olegamobile/sheriff3d/chez_downloads/calife_article_coinb.GIF

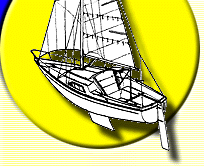
chez_downloads/calife_article_coinb.GIF
