olegamobile/sheriff3d/downloaded_assets/assets/photos/axesafran.jpg

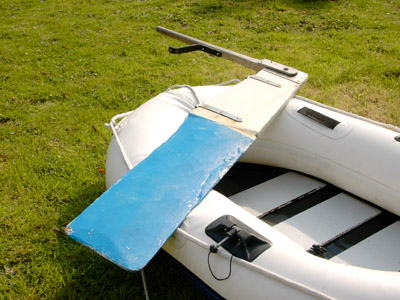
downloaded_assets/assets/photos/axesafran.jpg
