olegamobile/sheriff3d/downloaded_assets/assets/photos/Constance_I.jpg

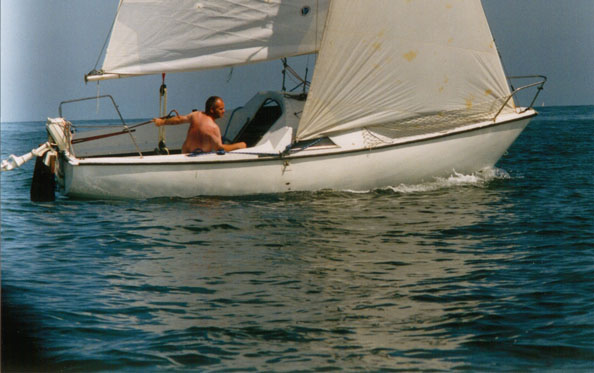
downloaded_assets/assets/photos/Constance_I.jpg
