olegamobile/sheriff3d/downloaded_assets/assets/photos/farfelu.jpg

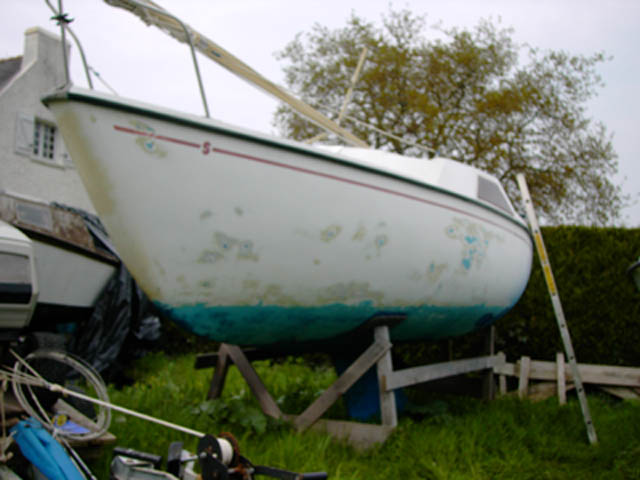
downloaded_assets/assets/photos/farfelu.jpg
