olegamobile/sheriff3d/downloaded_assets/assets/photos/ladesirade.jpg

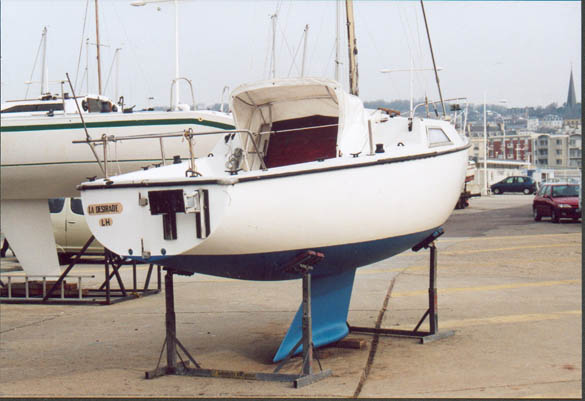
downloaded_assets/assets/photos/ladesirade.jpg
