olegamobile/sheriff3d/downloaded_assets/assets/photos/mouillage_Aix.jpg

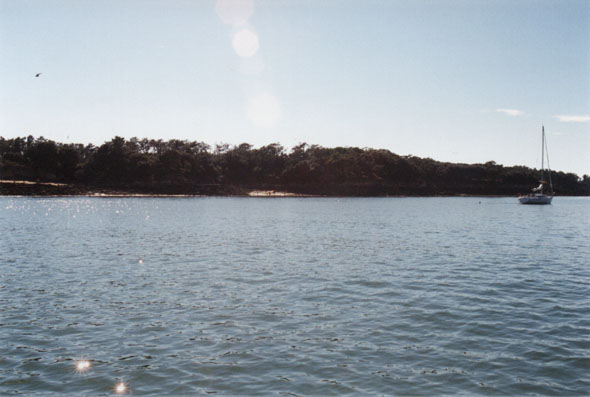
downloaded_assets/assets/photos/mouillage_Aix.jpg
