olegamobile/sheriff3d/downloaded_assets/assets/photos/mouro1.jpg

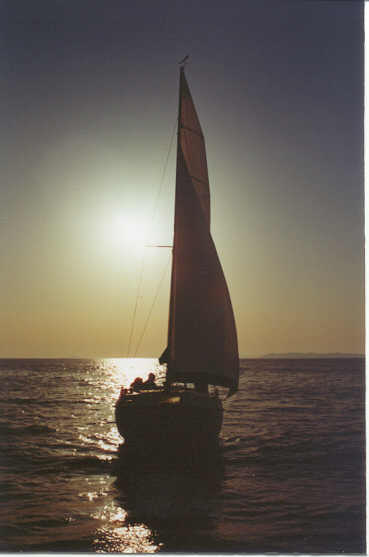
downloaded_assets/assets/photos/mouro1.jpg
