olegamobile/sheriff3d/downloaded_assets/assets/photos/mouro2.jpg

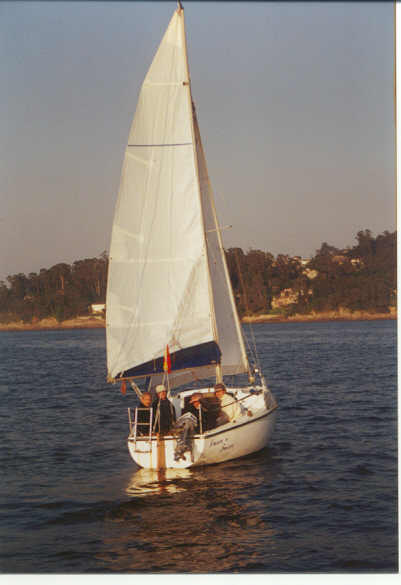
downloaded_assets/assets/photos/mouro2.jpg
