olegamobile/sheriff3d/downloaded_assets/assets/photos/noddi1.jpg

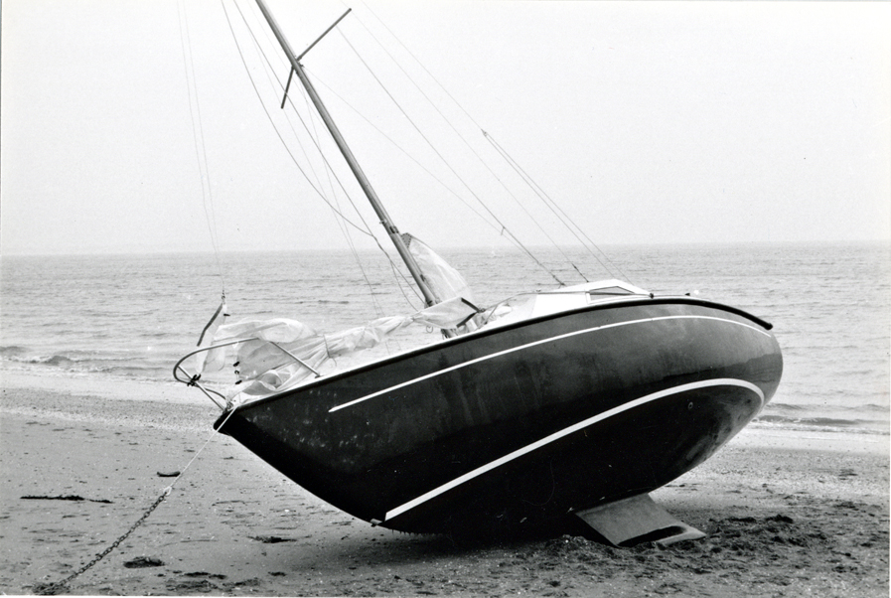
downloaded_assets/assets/photos/noddi1.jpg
