olegamobile/sheriff3d/downloaded_assets/assets/photos/noddi2.jpg

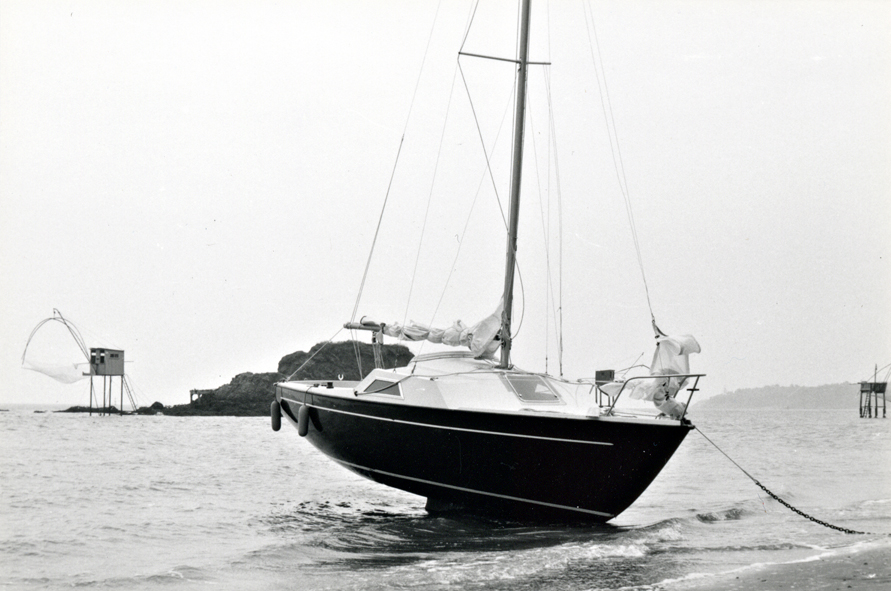
downloaded_assets/assets/photos/noddi2.jpg
