olegamobile/sheriff3d/downloaded_assets/assets/photos/port_RT_Arriere.jpg

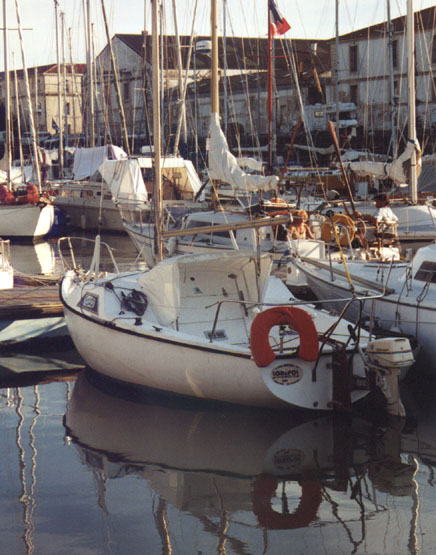
downloaded_assets/assets/photos/port_RT_Arriere.jpg
