olegamobile/sheriff3d/downloaded_assets/assets/photos/port_RT_pont.jpg

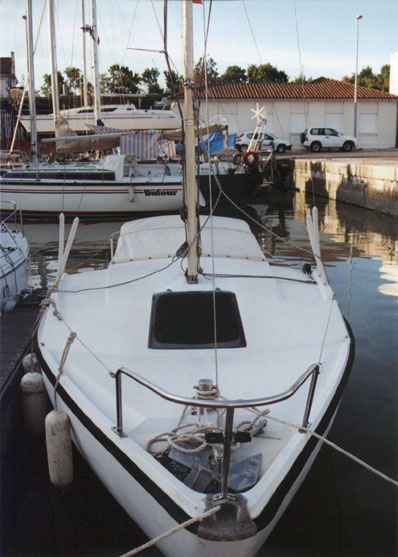
downloaded_assets/assets/photos/port_RT_pont.jpg
