olegamobile/sheriff3d/downloaded_assets/assets/photos/samoa_ii.jpg

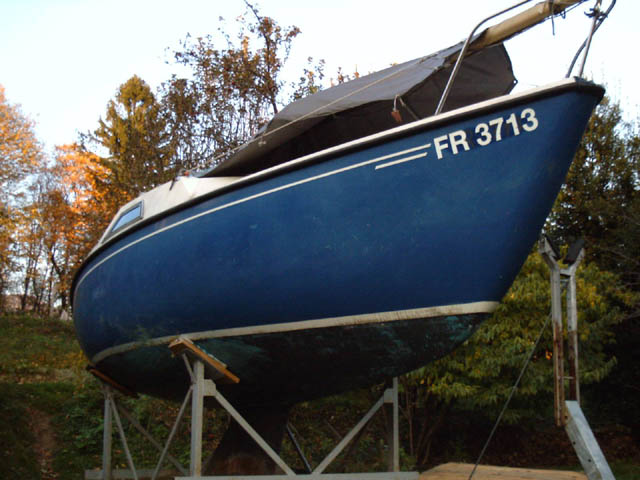
downloaded_assets/assets/photos/samoa_ii.jpg
