olegamobile/sheriff3d/extracted_pdf_assets/Bateaux_jui73/p1_1__im1.png

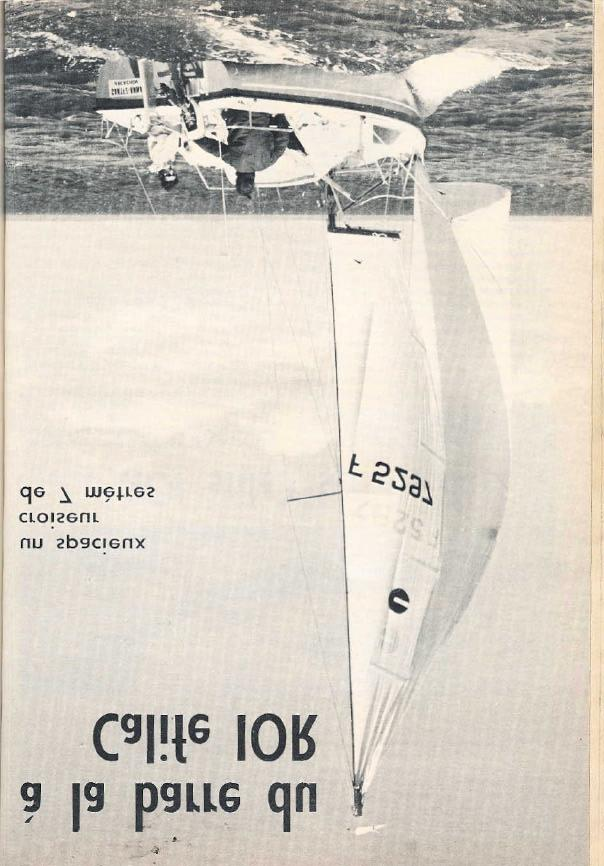
extracted_pdf_assets/Bateaux_jui73/p1_1__im1.png
