olegamobile/sheriff3d/extracted_pdf_assets/Bateaux_jui73/p1_corrected.png

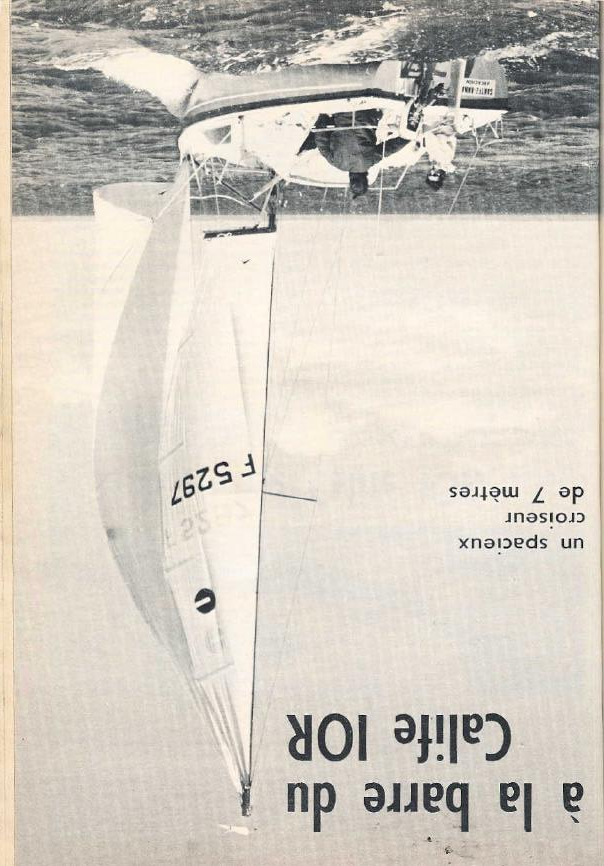
extracted_pdf_assets/Bateaux_jui73/p1_corrected.png
