olegamobile/sheriff3d/extracted_pdf_assets/Bateaux_jui73/p2_1__im2.png

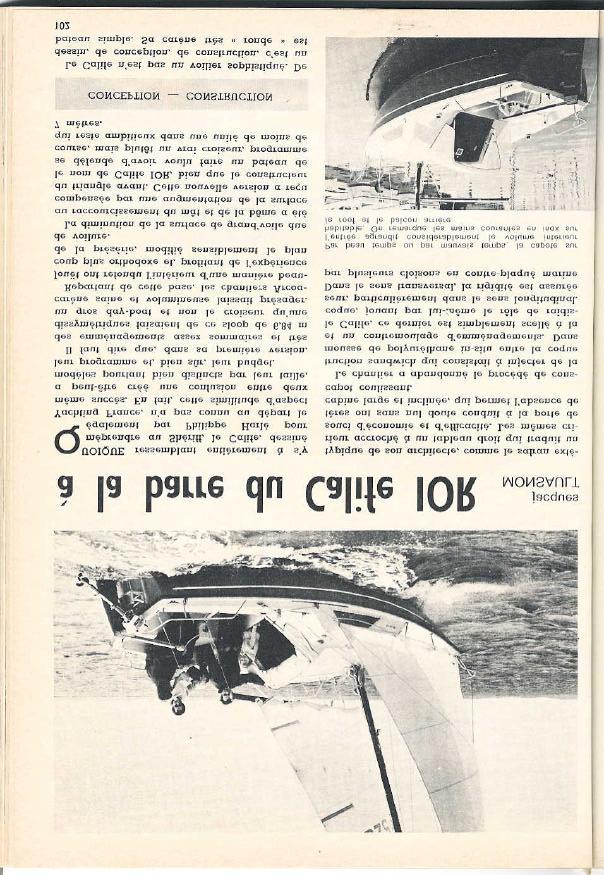
extracted_pdf_assets/Bateaux_jui73/p2_1__im2.png
