olegamobile/sheriff3d/extracted_pdf_assets/Bateaux_jui73/p3_1__im3.png

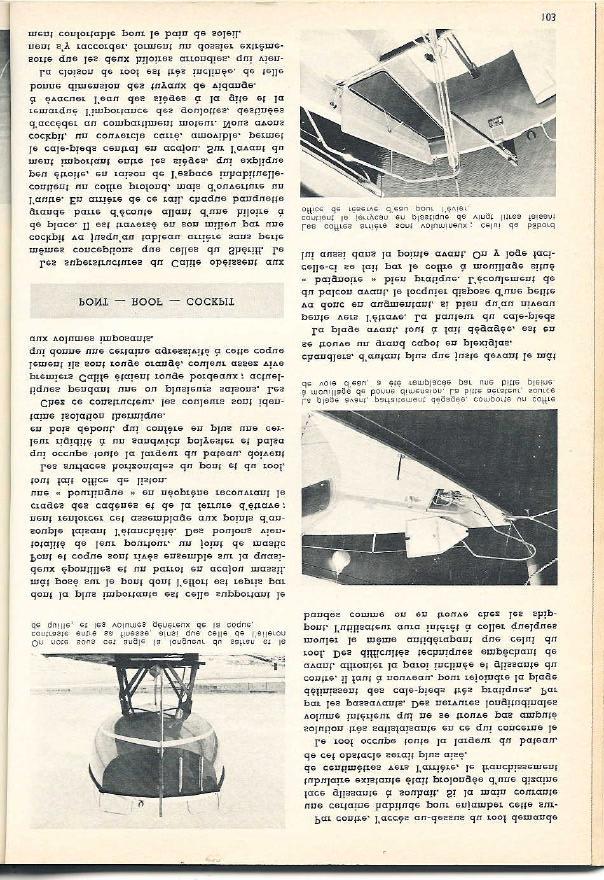
extracted_pdf_assets/Bateaux_jui73/p3_1__im3.png
