olegamobile/sheriff3d/extracted_pdf_assets/Bateaux_jui73/p7_1__im7.png

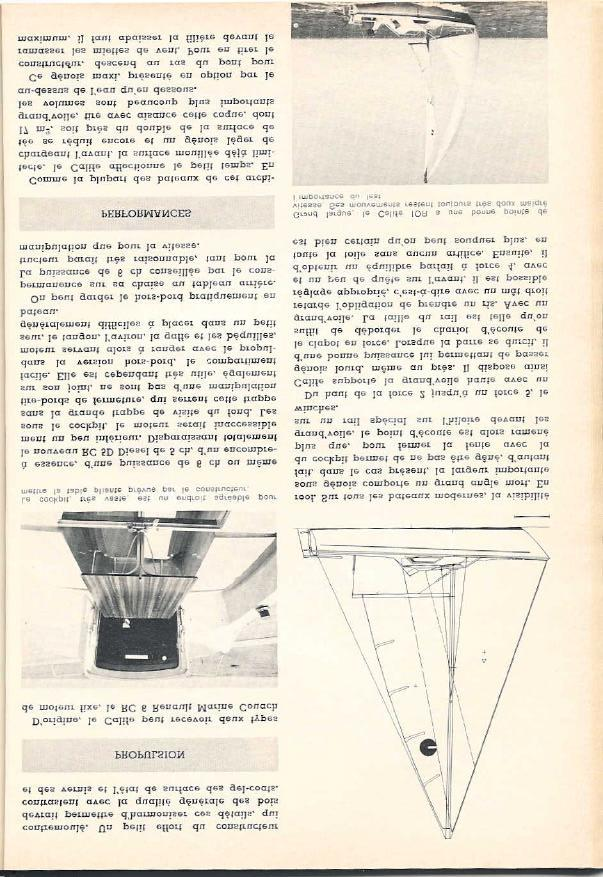
extracted_pdf_assets/Bateaux_jui73/p7_1__im7.png
