olegamobile/sheriff3d/extracted_pdf_assets/Bateaux_jui73/p8_1__im8.png

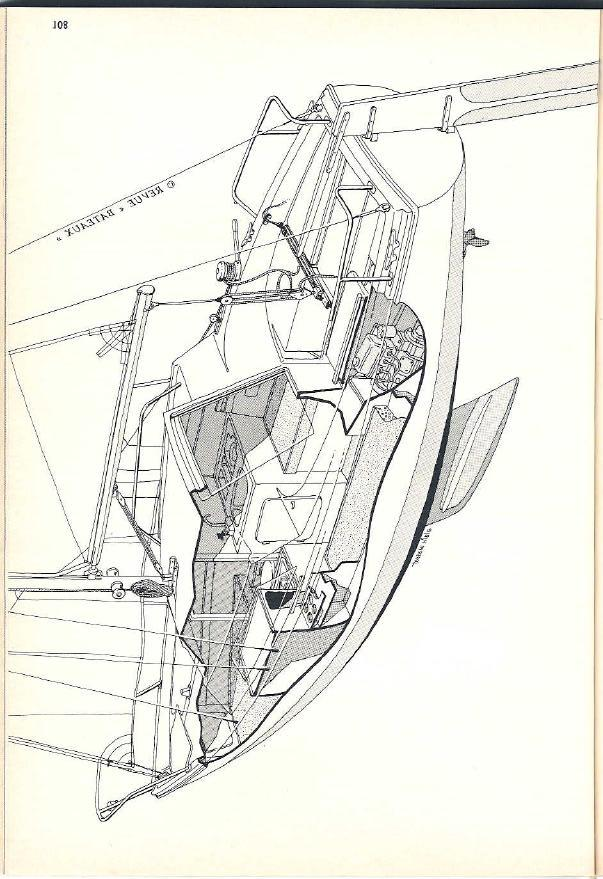
extracted_pdf_assets/Bateaux_jui73/p8_1__im8.png
