olegamobile/sheriff3d/extracted_pdf_assets/Bateaux_jui73/p10_1__im10.png

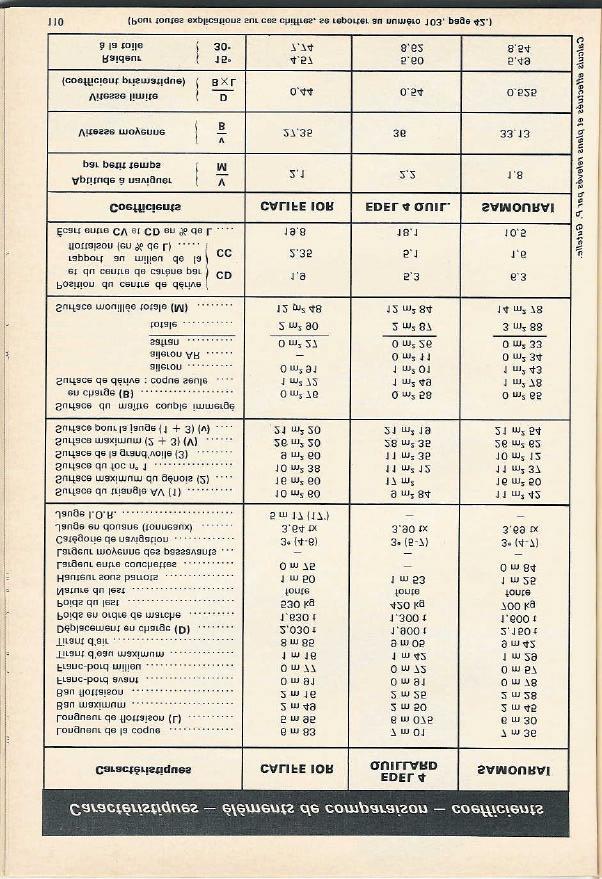
extracted_pdf_assets/Bateaux_jui73/p10_1__im10.png
