olegamobile/sheriff3d/extracted_pdf_assets/Bateaux_oct69/annotated_body_plan.png

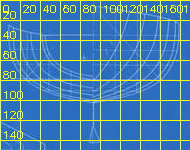
extracted_pdf_assets/Bateaux_oct69/annotated_body_plan.png
