olegamobile/sheriff3d/extracted_pdf_assets/Bateaux_oct69/annotated_half_breadth.png

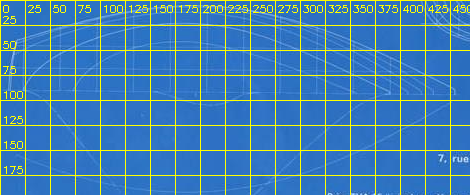
extracted_pdf_assets/Bateaux_oct69/annotated_half_breadth.png
