olegamobile/sheriff3d/extracted_pdf_assets/Bateaux_oct69/annotated_profile.png

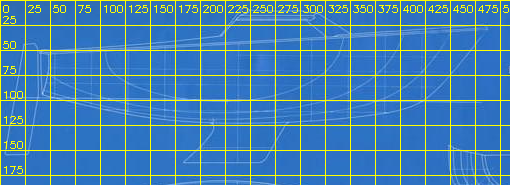
extracted_pdf_assets/Bateaux_oct69/annotated_profile.png
