olegamobile/sheriff3d/extracted_pdf_assets/Bateaux_oct69/crop_half_breadth.png

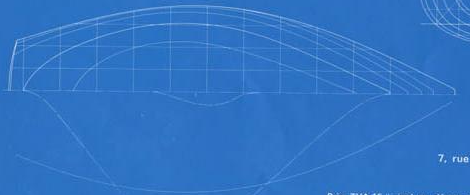
extracted_pdf_assets/Bateaux_oct69/crop_half_breadth.png
