olegamobile/sheriff3d/extracted_pdf_assets/Bateaux_oct69/crop_profile.png

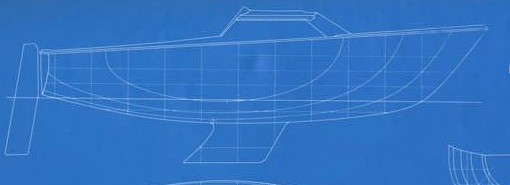
extracted_pdf_assets/Bateaux_oct69/crop_profile.png
