olegamobile/sheriff3d/extracted_pdf_assets/Bateaux_oct69/lines_plan_oriented.png

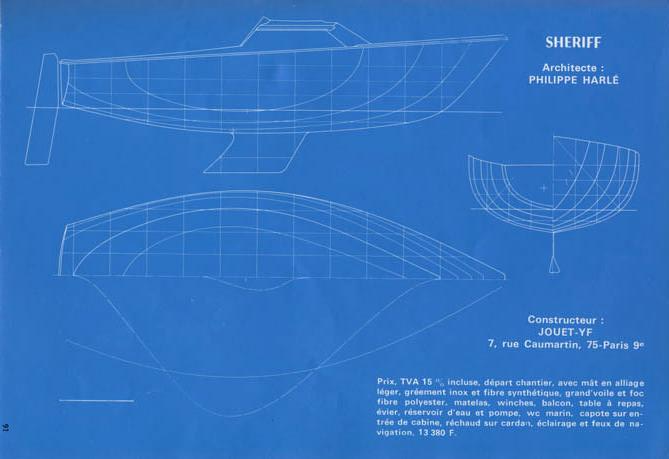
extracted_pdf_assets/Bateaux_oct69/lines_plan_oriented.png
