olegamobile/sheriff3d/extracted_pdf_assets/Bateaux_oct69/p1_1__im1.png

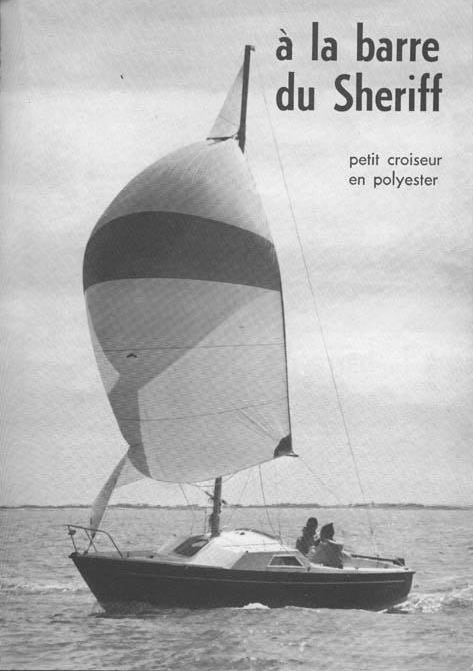
extracted_pdf_assets/Bateaux_oct69/p1_1__im1.png
