olegamobile/sheriff3d/extracted_pdf_assets/Bateaux_oct69/p4_1__im4.png

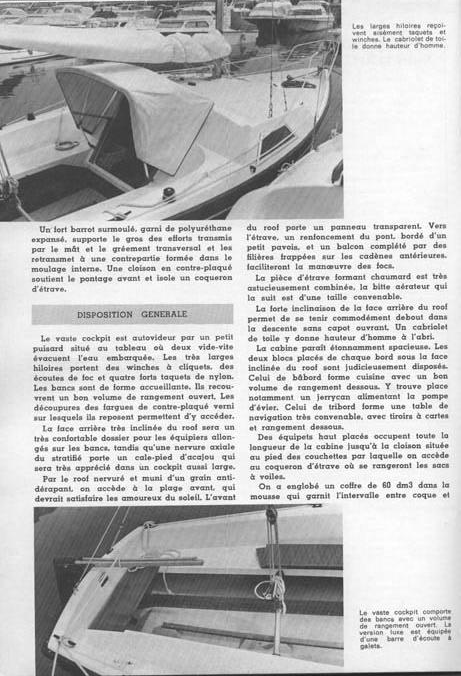
extracted_pdf_assets/Bateaux_oct69/p4_1__im4.png
