olegamobile/sheriff3d/extracted_pdf_assets/Bateaux_oct69/p5_1__im5.png

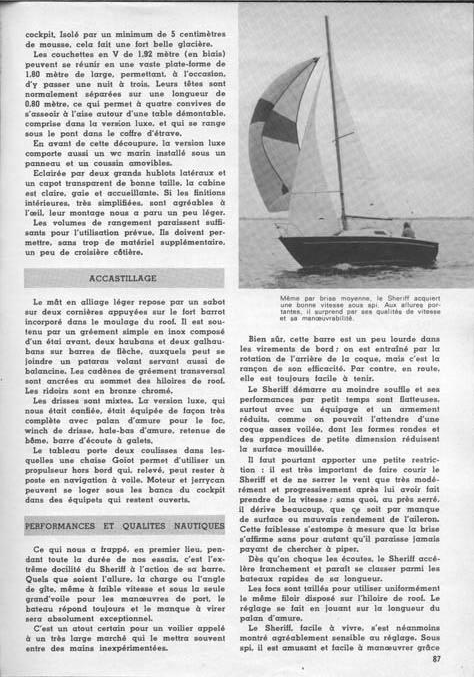
extracted_pdf_assets/Bateaux_oct69/p5_1__im5.png
