olegamobile/sheriff3d/extracted_pdf_assets/Bateaux_oct69/p6_1__im6.png

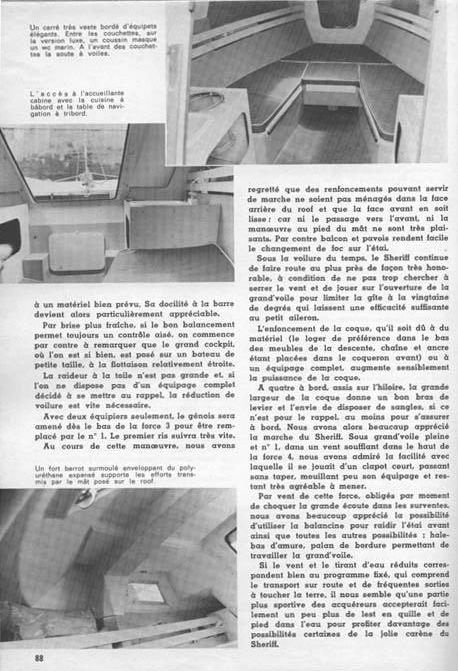
extracted_pdf_assets/Bateaux_oct69/p6_1__im6.png
