olegamobile/sheriff3d/extracted_pdf_assets/Bateaux_oct69/p9_1__im9.png

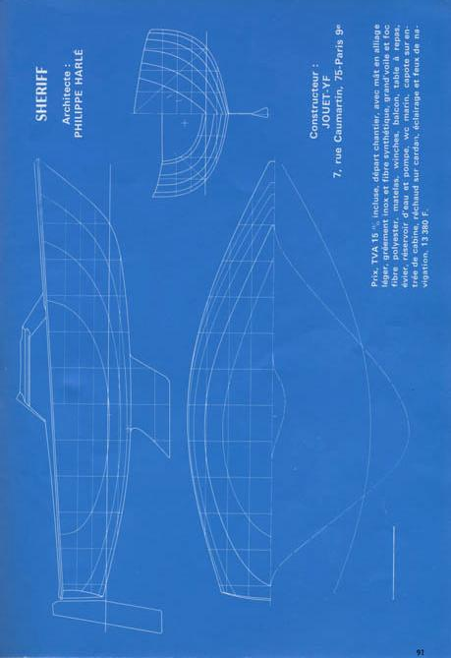
extracted_pdf_assets/Bateaux_oct69/p9_1__im9.png
