olegamobile/sheriff3d/extracted_pdf_assets/Bateaux_oct69/p11_1__im11.png

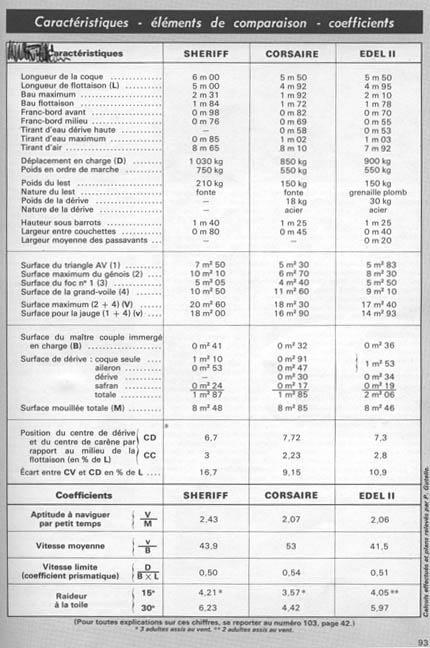
extracted_pdf_assets/Bateaux_oct69/p11_1__im11.png
