olegamobile/sheriff3d/extracted_pdf_assets/Bateaux_oct69/white_lines.png

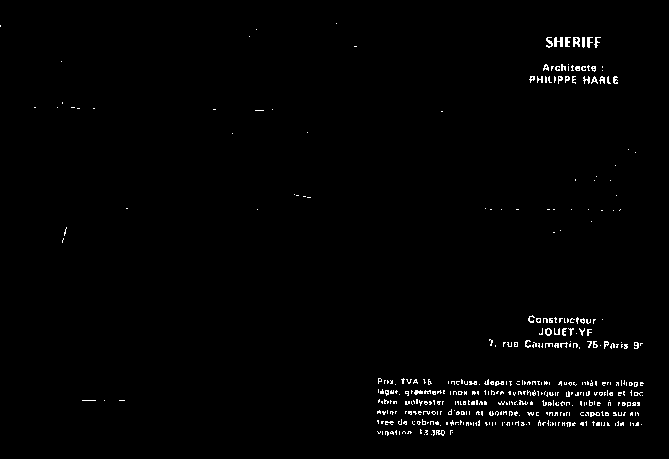
extracted_pdf_assets/Bateaux_oct69/white_lines.png
