olegamobile/sheriff3d/extracted_pdf_assets/manuel/p2_1__im1.png

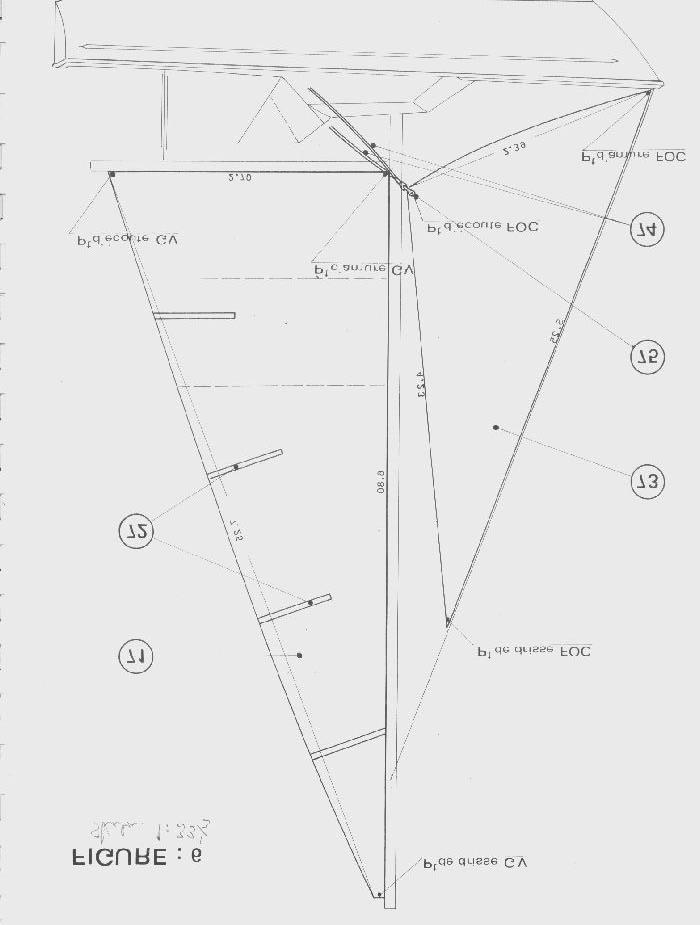
extracted_pdf_assets/manuel/p2_1__im1.png
