olegamobile/sheriff3d/extracted_pdf_assets/manuel/p3_1__im2.png

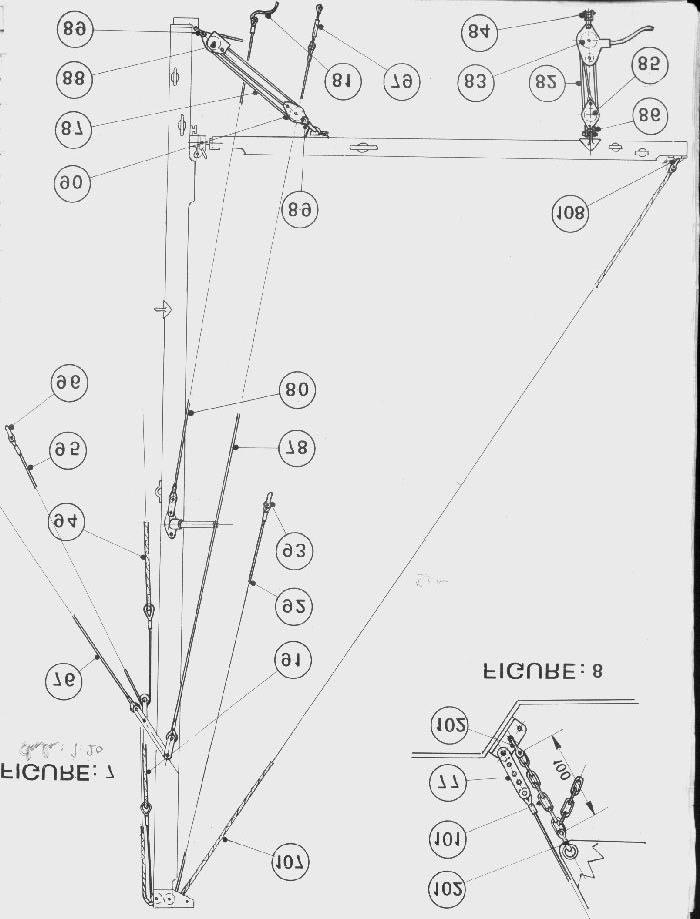
extracted_pdf_assets/manuel/p3_1__im2.png
