olegamobile/sheriff3d/extracted_pdf_assets/manuel/p4_1__im3.png

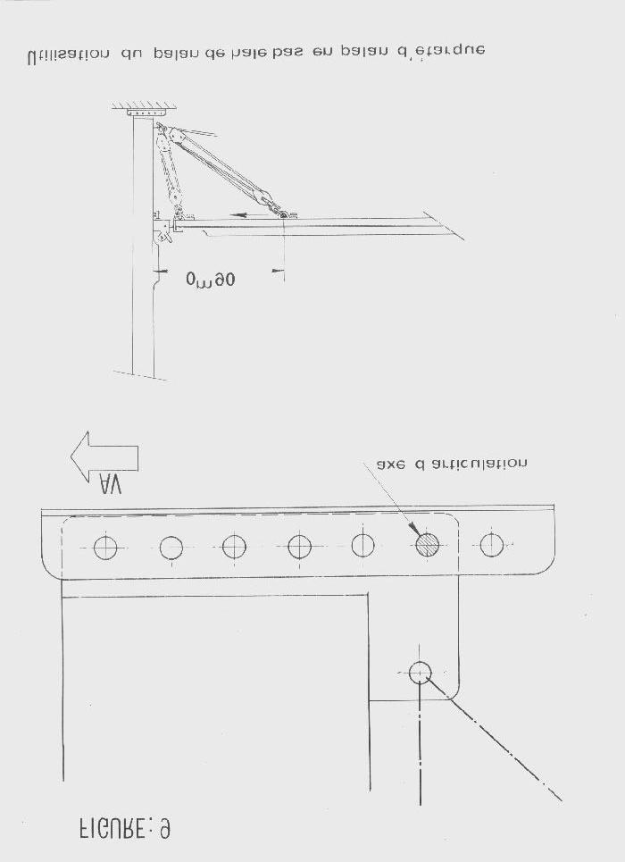
extracted_pdf_assets/manuel/p4_1__im3.png
