olegamobile/sheriff3d/extracted_pdf_assets/manuel/p5_1__im4.png

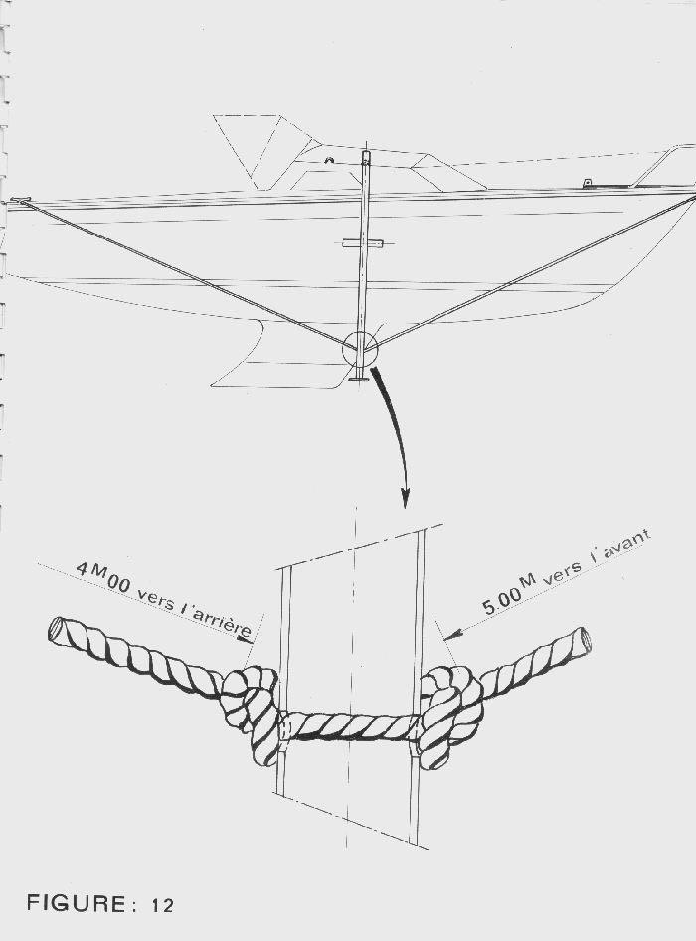
extracted_pdf_assets/manuel/p5_1__im4.png
