olegamobile/sheriff3d/extracted_pdf_assets/manuel/p6_1__im5.png

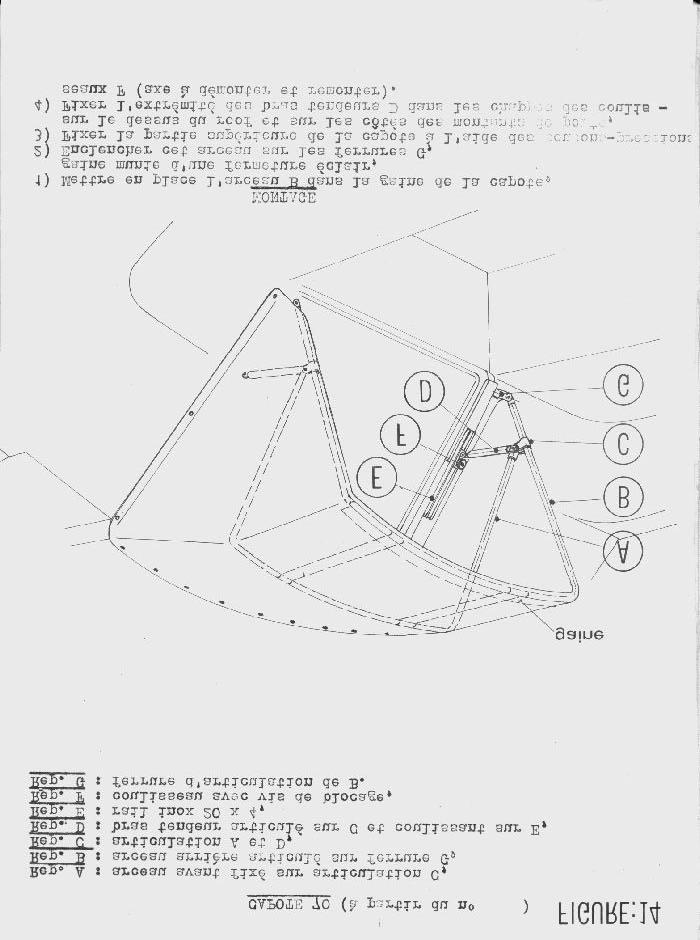
extracted_pdf_assets/manuel/p6_1__im5.png
