olegamobile/sheriff3d/extracted_pdf_assets/manuel/p7_1__im6.png

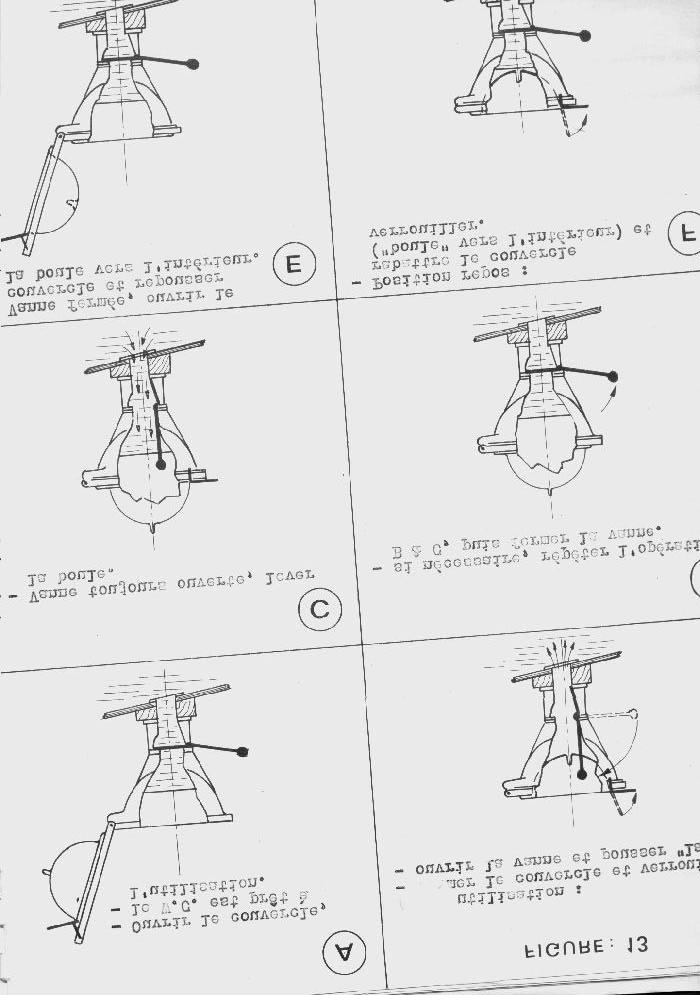
extracted_pdf_assets/manuel/p7_1__im6.png
