olegamobile/sheriff3d/extracted_pdf_assets/manuel/p8_1__im7.png

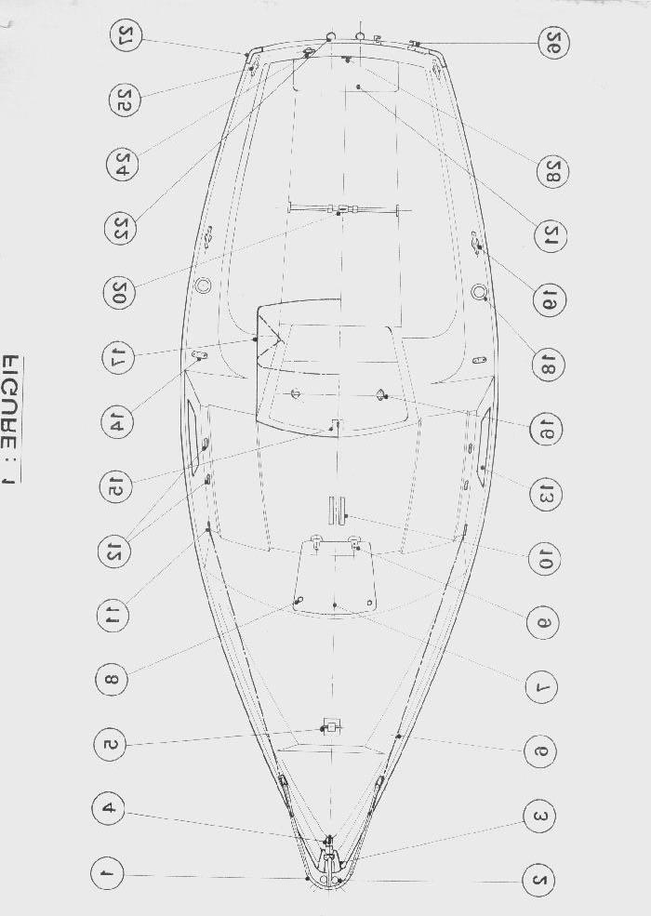
extracted_pdf_assets/manuel/p8_1__im7.png
