olegamobile/sheriff3d/extracted_pdf_assets/manuel/p10_1__im8.png

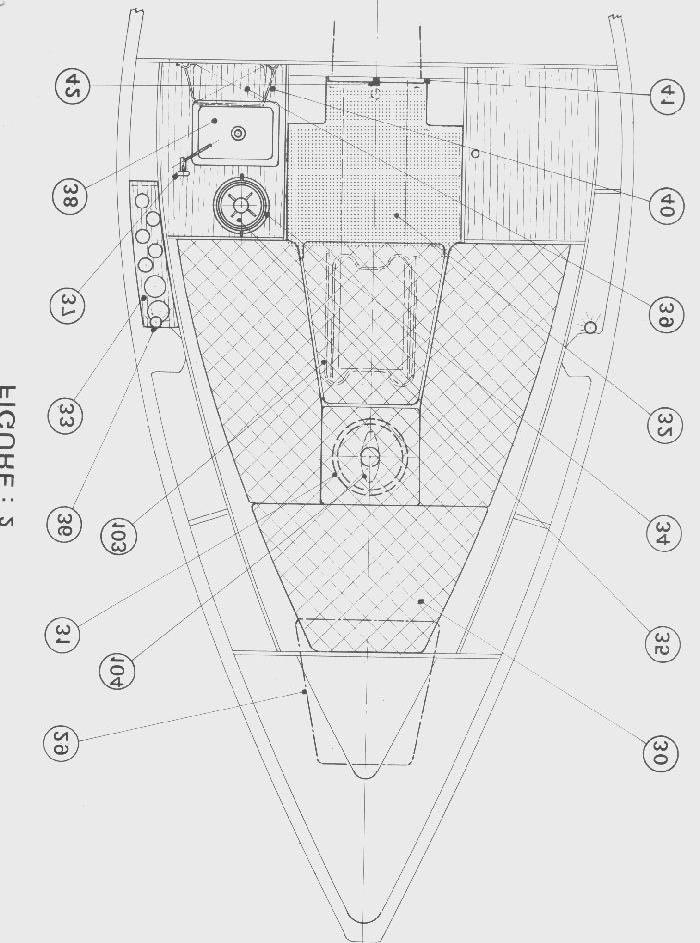
extracted_pdf_assets/manuel/p10_1__im8.png
