olegamobile/sheriff3d/extracted_pdf_assets/manuel/p12_1__im9.png

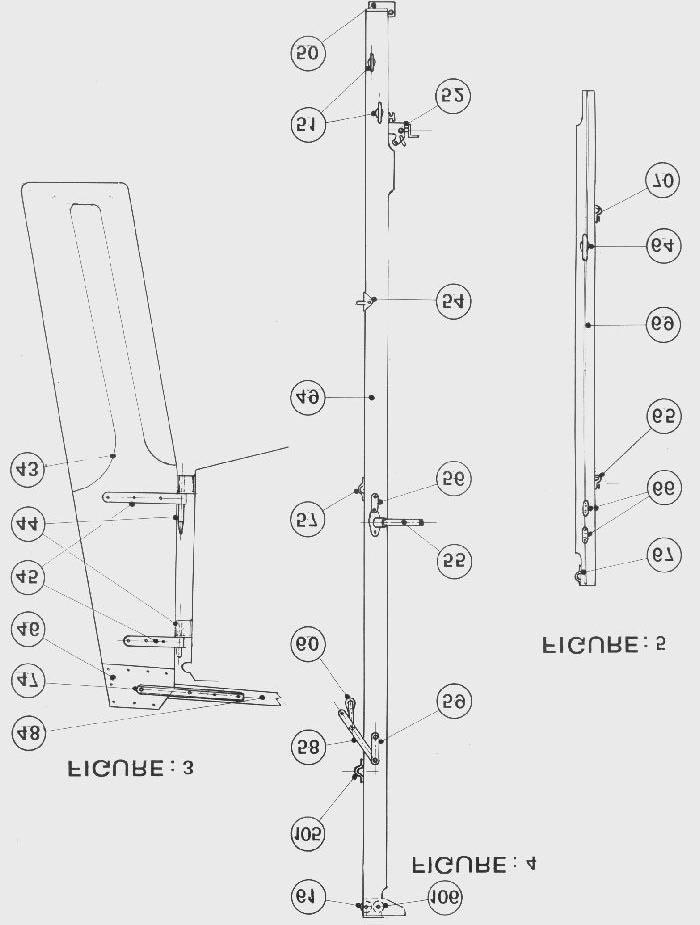
extracted_pdf_assets/manuel/p12_1__im9.png
