olegamobile/sheriff3d/extracted_pdf_assets/manuel/p15_1__im10.png

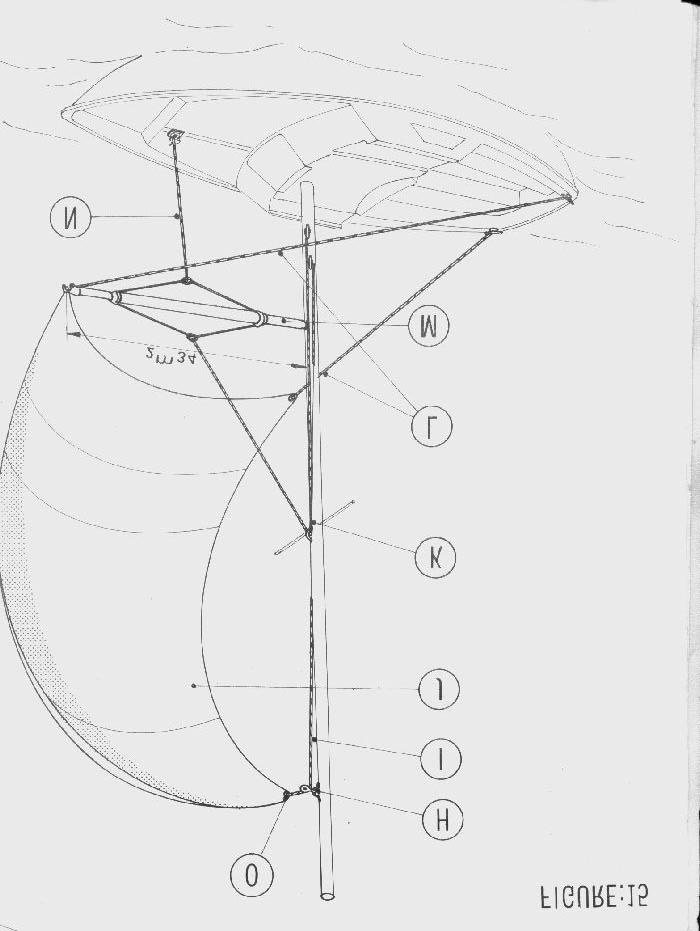
extracted_pdf_assets/manuel/p15_1__im10.png
