olegamobile/sheriff3d/real_photos/photo_2026-09-10_22-20-59.jpg

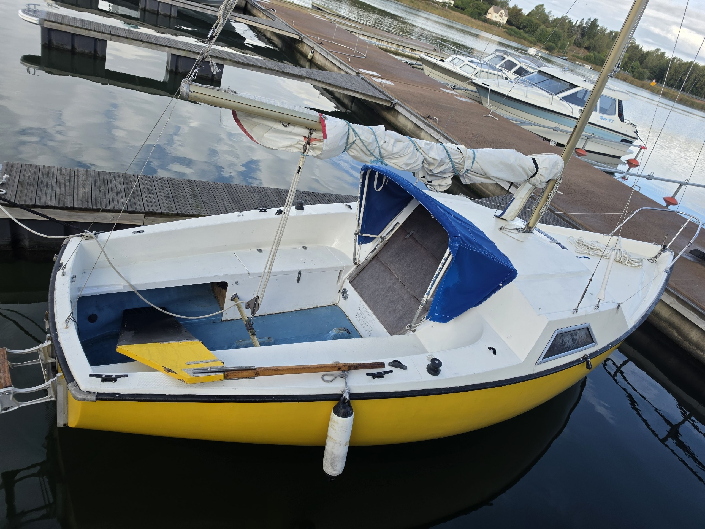
real_photos/photo_2026-09-10_22-20-59.jpg
