olegamobile/sheriff3d/real_photos/photo_2026-09-10_22-21-10.jpg

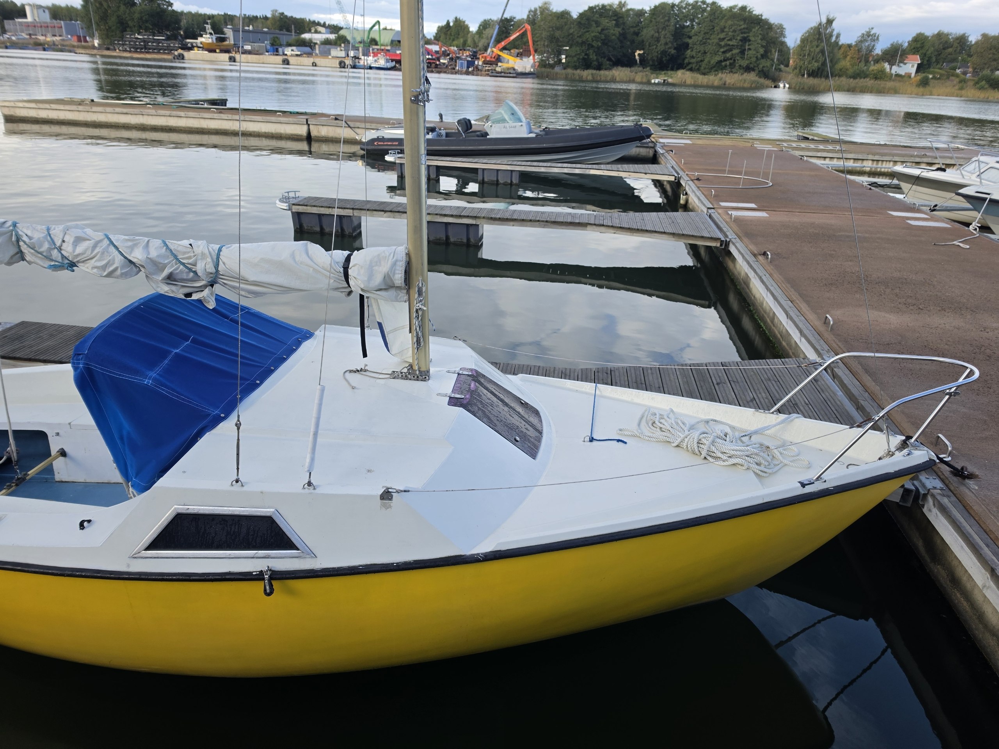
real_photos/photo_2026-09-10_22-21-10.jpg
