olegamobile/sheriff3d/downloaded_assets/assets/manual/interieur.jpg

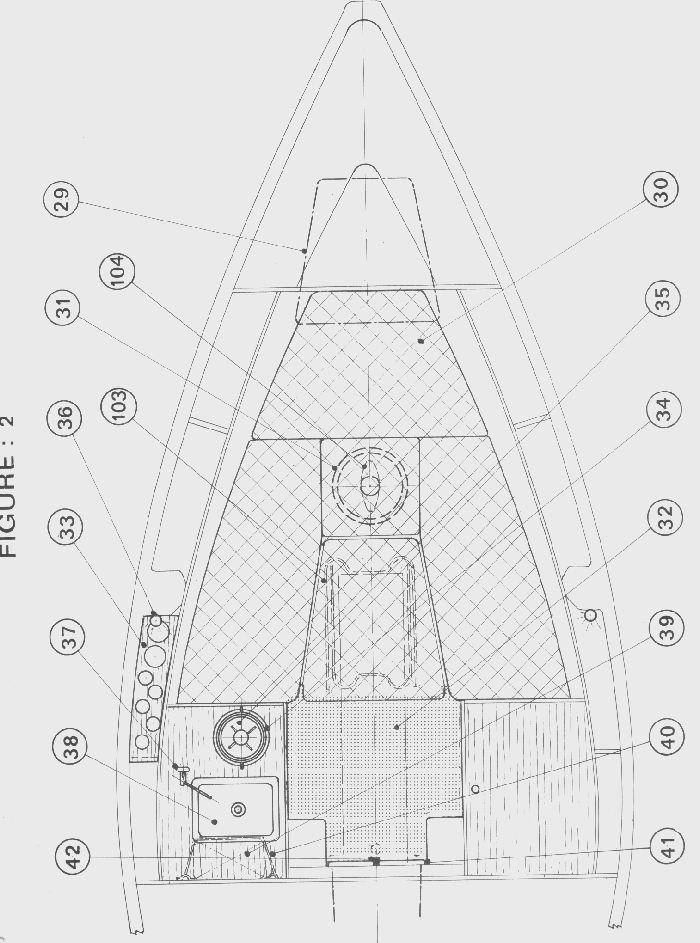
downloaded_assets/assets/manual/interieur.jpg
