olegamobile/sheriff3d/downloaded_assets/assets/manual/pied.jpg

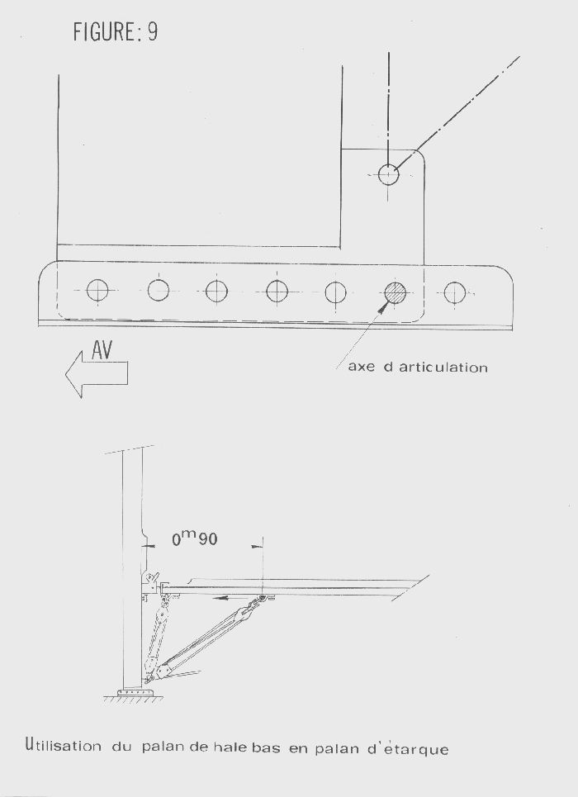
downloaded_assets/assets/manual/pied.jpg
