olegamobile/sheriff3d/downloaded_assets/assets/manual/spi.gif

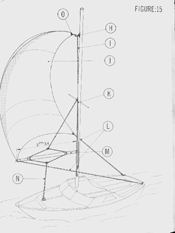
downloaded_assets/assets/manual/spi.gif
