olegamobile/sheriff3d/downloaded_assets/assets/manual/voiles.jpg

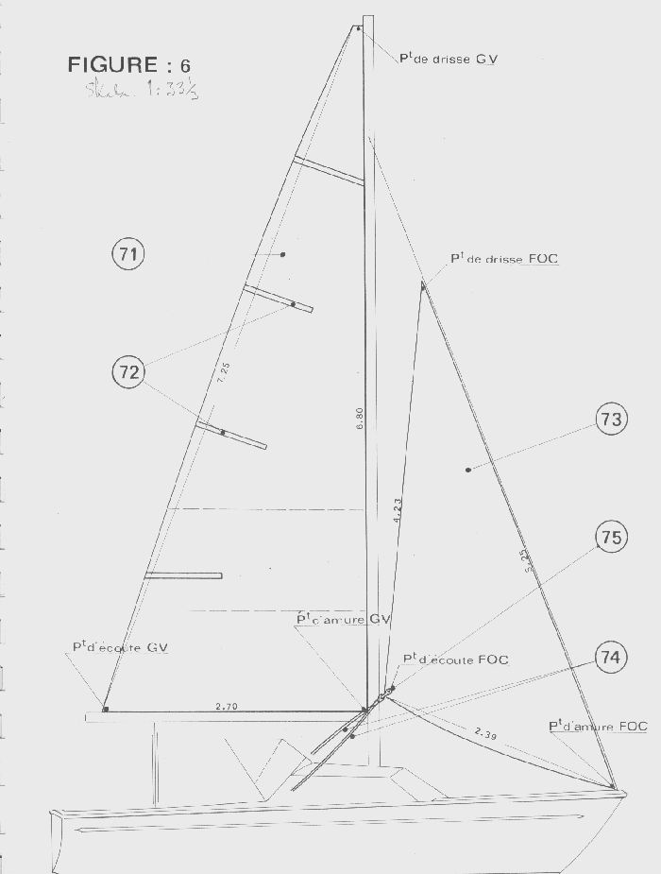
downloaded_assets/assets/manual/voiles.jpg
