olegamobile/sheriff3d/test_deck_top_view.png

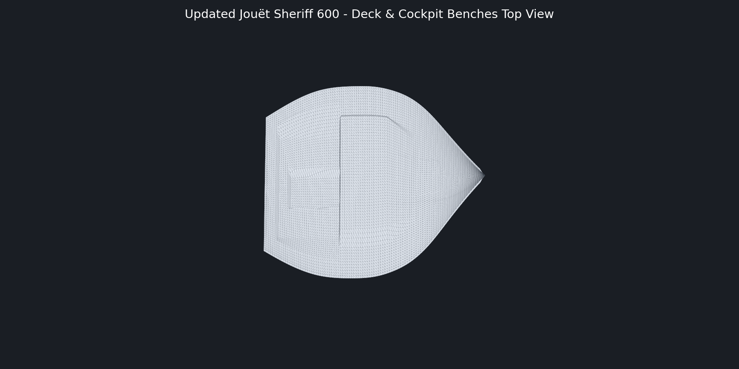
test_deck_top_view.png
