olegamobile/sheriff3d/test_v3_renders.png

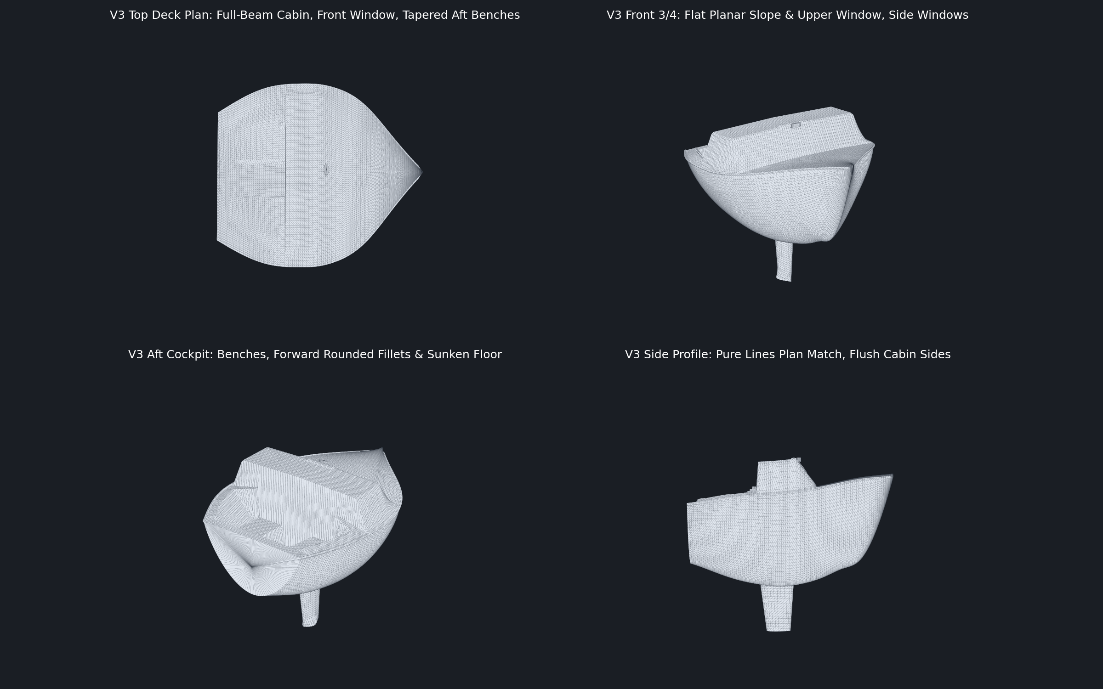
test_v3_renders.png
